silverstee1/SP1ETH/Kicad/ConnSP1.kicad_sch

## KiCad design Kicad/ConnSP1.kicad_sch (2025-02-01)

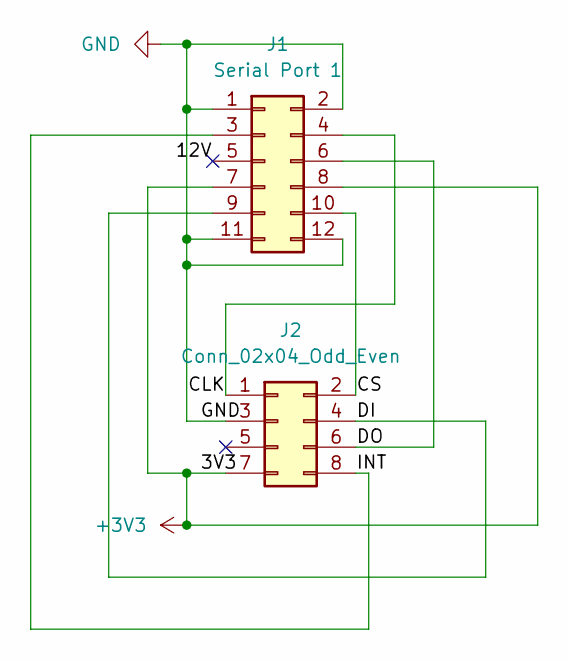
[picture p9: schematic ConnSP1.kicad_sch]

Parts:
J1: Serial Port 1; SP1_FootPrint
J2: Conn_02x04_Odd_Even; PinHeader_2x04_P2.54mm_Vertical

Connections:
12V: J1.5
+3V3: J1.7, J1.8, J2.7
CLK: J1.4, J2.1
CS: J1.10, J2.2
DI: J1.9, J2.4
DO: J1.6, J2.6
GND: J1.1, J1.2, J1.11, J1.12, J2.3
INT: J1.3, J2.8
